Frapais/Canopy-Environmental-and-Presence-module/Images/image15.jpg

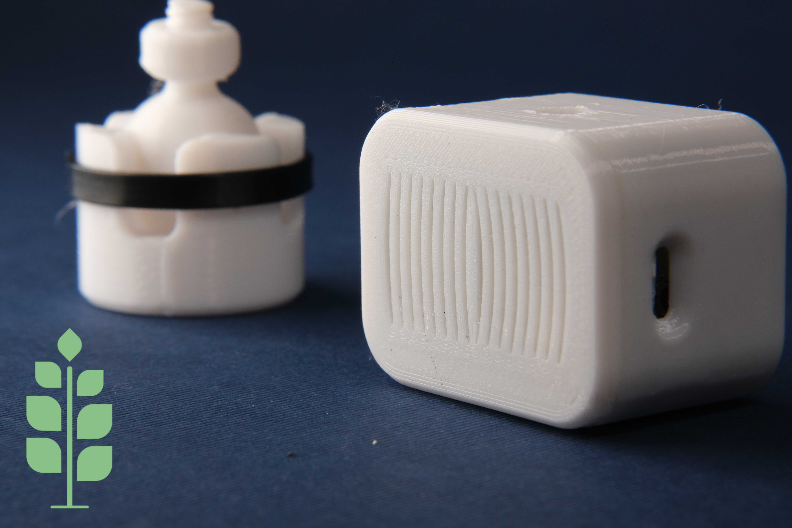
Images/image15.jpg
