Frapais/Canopy-Environmental-and-Presence-module/Images/image16.jpg

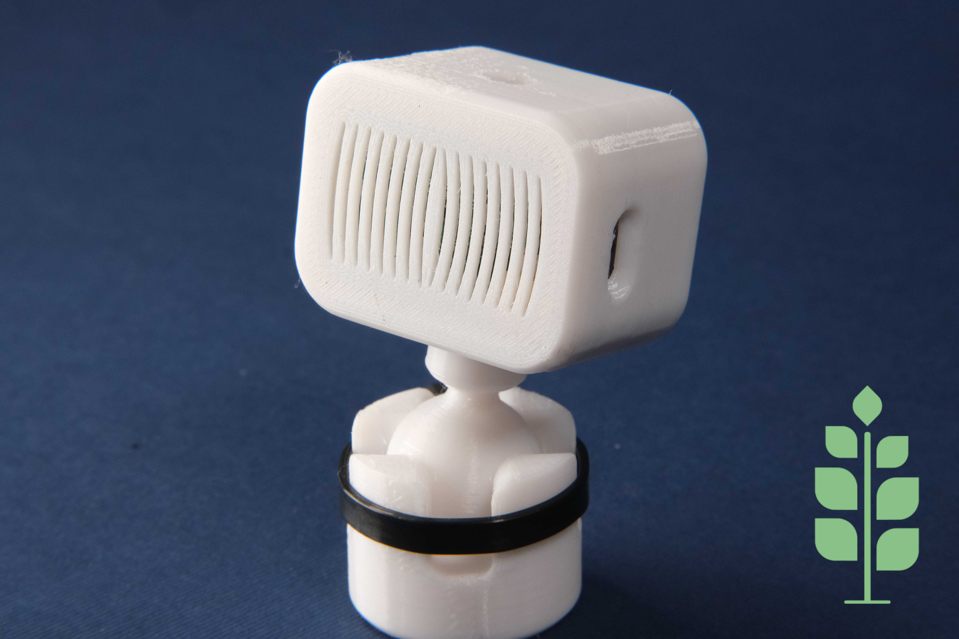
Images/image16.jpg
